MingyaoLiu/CMStormSwitchTesterMacroKeyboard/IMG_0317.jpg

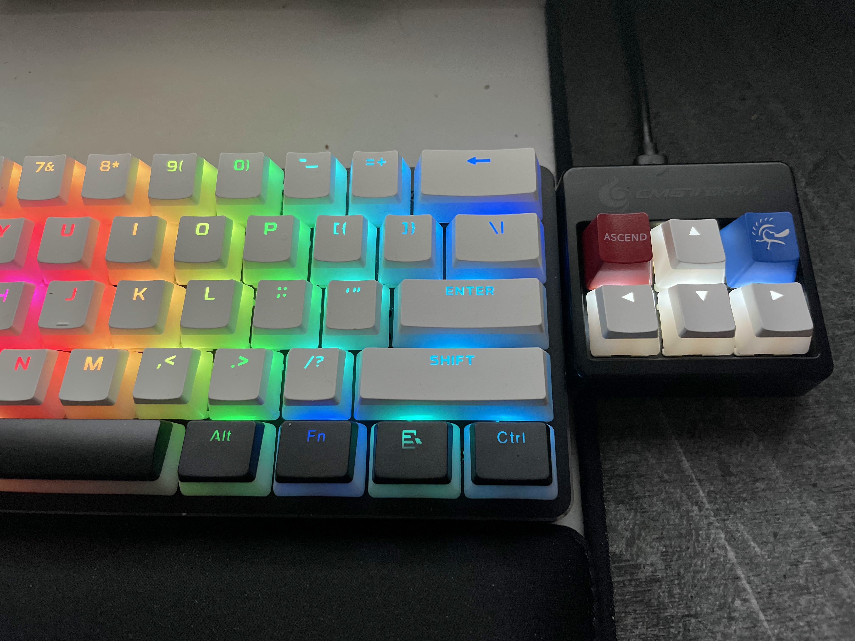
IMG_0317.jpg
